MOSH-Insa-Toulouse/2023-2024-4GP-DOYHENARD-KEMPF/LTSpice/Capteur_Graphite.asc

B1: bi; I=V(cp,cn)*(10n+(v(gc,gn)*10n))
C: cap; 200p
R: res; 1k
Named nets: gp, gn, gc, cp, cn
