MOSH-Insa-Toulouse/2023-2024-4GP-DOYHENARD-KEMPF/LTSpice/Circuit_ampli_Projet_Capteur.asc

C1: cap; 100n
C2: cap; 100n
C3: cap; 100n
C4: cap; 1µ
C5: cap; 1p
R1: res; 100k
R2: res; 1k
R3: res; 100k
R5: res; 10k
R6: res; 1k
U1: LTC1050
V1: voltage; 5
V2: voltage; SINE(0 325 50)
V3: voltage; PULSE(0 1 0.2 0.1 0.1 20); AC 1 0
X1: Capteur_Graphite
Named nets: 0, ADC
.ac oct 200 0.1 100k
.param G0 10n
.param G1 10n
.param R1 1k
.trans 20
